DanielFLopez1620/G-Mov_Project/g_mov_description/meshes/picam.stl

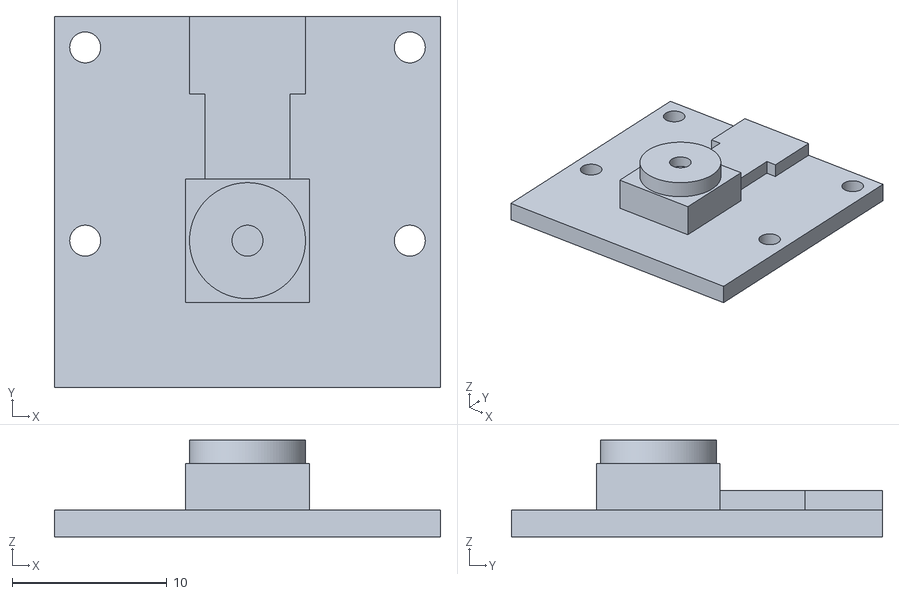
[picture p13: CAD file, 2025-04-10]
g_mov_description/meshes/picam.stl
25.0 x 24.0 x 6.25
