DanielFLopez1620/G-Mov_Project/g_mov_description/meshes/picam_sup.stl

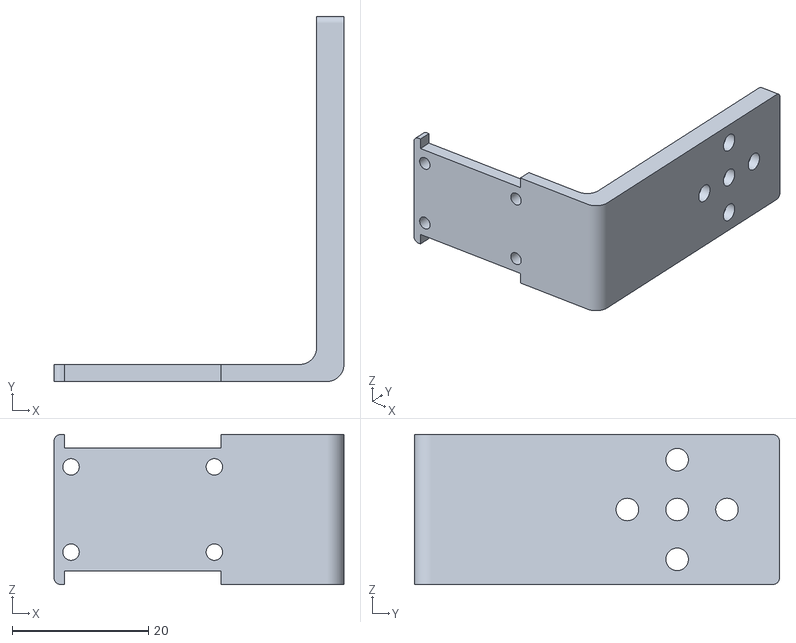
[picture p14: CAD file, 2025-04-10]
g_mov_description/meshes/picam_sup.stl
42.5 x 53.5 x 22.0
